AxesOfEvil/VW_MkVI_Dynaudio/CanMsg.h

const struct can_frame canMsg_AmpEnable[18] = {
  {0x6C7,0x2,0x1B,0x42,0x00,0x00,0x00,0x00,0x00,0x00},
  {0x6C7,0x2,0x1B,0x43,0x00,0x00,0x00,0x00,0x00,0x00},
  {0x6C7,0x2,0x1B,0x41,0x00,0x00,0x00,0x00,0x00,0x00},
  {0x6C7,0x3,0x2B,0x50,0x01,0x00,0x00,0x00,0x00,0x00},
  {0x6C7,0x3,0x2B,0x53,0x00,0x00,0x00,0x00,0x00,0x00},
  {0x6C7,0x8,0x80,0x07,0x2B,0x55,0x78,0x00,0x00,0x00},
  {0x6C7,0x4,0xC0,0x22,0x22,0x00,0x00,0x00,0x00,0x00},
  {0x6C7,0x8,0x80,0x07,0x2B,0x51,0x00,0x00,0x04,0x05},
  {0x6C7,0x4,0xC0,0x0A,0x08,0xFF,0x00,0x00,0x00,0x00},
  {0x6C7,0x7,0x80,0x03,0x1B,0x52,0x00,0x00,0x0D,0x00},
  {0x6C7,0x7,0x80,0x03,0x1B,0x54,0x00,0x00,0x0D,0x00},
  {0x6C7,0x7,0x80,0x03,0x1B,0x57,0x00,0x00,0x0D,0x00},
  {0x6C7,0x7,0x80,0x03,0x1B,0x58,0x00,0x00,0x0D,0x00},
  {0x6C7,0x7,0x80,0x03,0x1B,0x59,0x00,0x00,0x0D,0x00},
  {0x6C7,0x7,0x80,0x03,0x1B,0x5A,0x00,0x00,0x0D,0x00},
  {0x6C7,0x7,0x80,0x03,0x1B,0x5B,0x00,0x00,0x0D,0x00},
  {0x6C7,0x7,0x80,0x03,0x1B,0x5C,0x00,0x00,0x04,0x00},
  {0x6C7,0x7,0x80,0x03,0x1B,0x5E,0x00,0x00,0x04,0x00},
};
const struct can_frame canMsg_AmpDisable = {
  0x6C7,0x3,0x2B,0x50,0x00,0x00,0x00,0x00,0x00,0x00
};
